f5AFfMhv/SOS_business_card/Design/Logism/generated_circuit.png

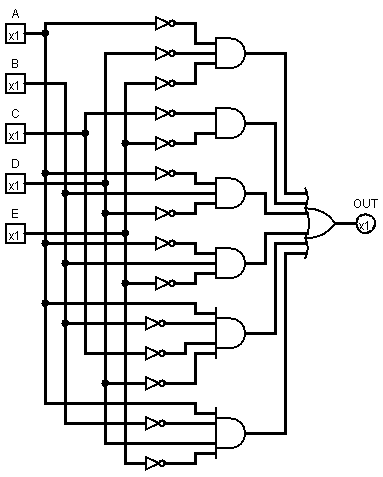
Design/Logism/generated_circuit.png
