f5AFfMhv/SOS_business_card/Design/Logism/truth_table.PNG

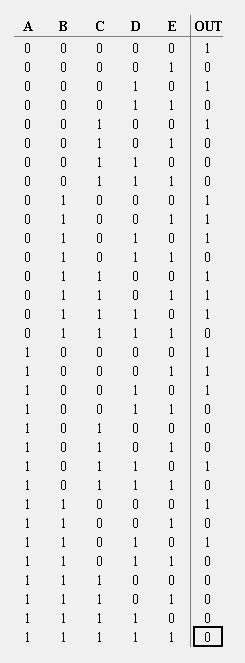
Design/Logism/truth_table.PNG
